kwikius/ultrasonic_wind_sensor/sensor_hardware/modified_reversing_sensor_circuit/filter.sch

## KiCad design sensor_hardware/modified_reversing_sensor_circuit/filter.sch (2021-09-10, an earlier design)

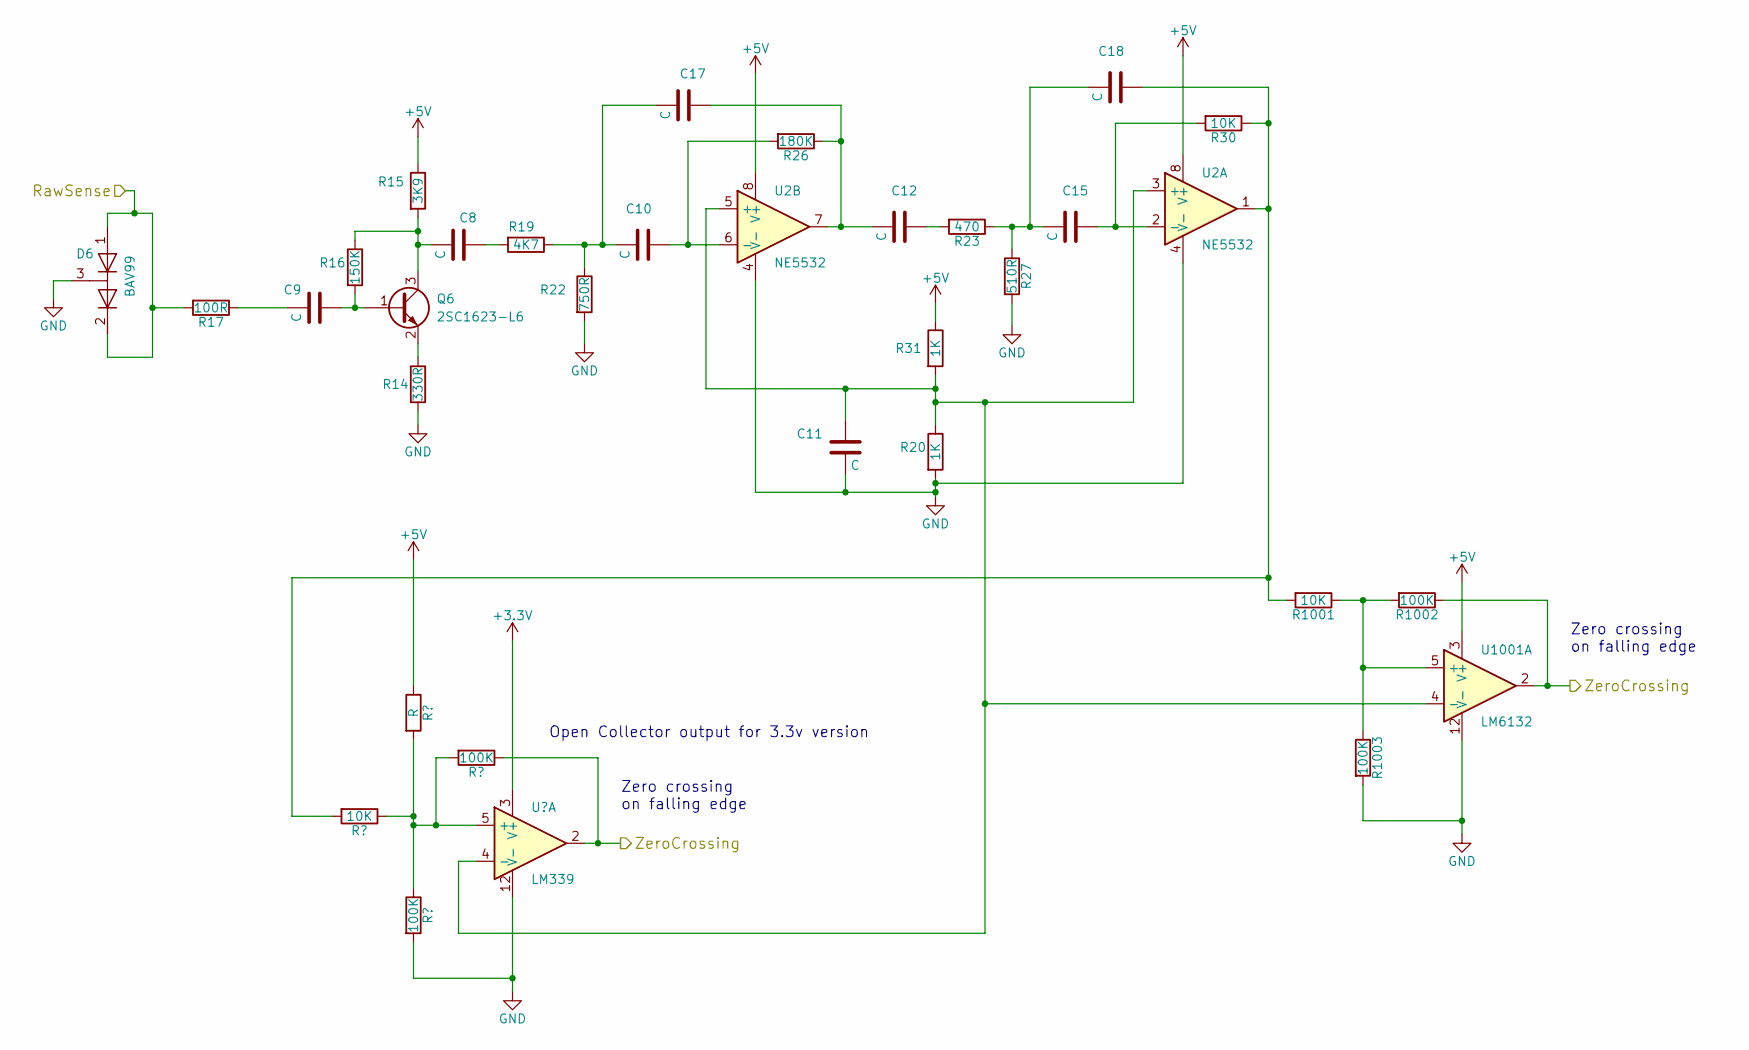
[picture p11: schematic filter.sch]

Parts:
C8, C9, C10, C11, C12, C15, C17, C18: C
D6: BAV99
Q6: 2SC1623-L6
R14: 330R
R15: 3K9
R16: 150K
R17: 100R
R19: 4K7
R20, R31: 1K
R22: 750R
R23: 470
R26: 180K
R27: 510R
R30, R1001: 10K
R1002, R1003: 100K
U2: NE5532
U1001: LM6132

Connections:
+5V: R15.1, R31.1, U2.8 (V+), U1001.3 (V+)
GND: C11.2, D6.3 (common), R14.2, R20.2, R22.2, R27.2, R1003.2, U2.4 (V-), U1001.12 (V-)
unnamed: C8.1, R19.2
unnamed: C8.2, Q6.3 (C), R15.2, R16.1
unnamed: C9.1, Q6.1 (B), R16.2
unnamed: C9.2, R17.1
unnamed: C10.1, R26.2, U2.6 (-)
unnamed: C10.2, C17.2, R19.1, R22.1
unnamed: C11.1, R20.1, R31.2, U2.3 (+), U2.5 (+), U1001.4 (-)
unnamed: C12.1, R23.2
unnamed: C12.2, C17.1, R26.1, U2.7
unnamed: C15.1, R30.2, U2.2 (-)
unnamed: C15.2, C18.2, R23.1, R27.1
unnamed: C18.1, R30.1, R1001.2, U2.1
unnamed: Q6.2 (E), R14.1
unnamed: R1001.1, R1002.2, R1003.1, U1001.5 (+)
RawSense: D6.1 (A), D6.2 (K), R17.2
ZeroCrossing: R1002.1, U1001.2

Notes on the sheet:
Zero crossing on falling edge
Open Collector output for 3.3v version
