kwikius/ultrasonic_wind_sensor/sensor_hardware/modified_reversing_sensor_circuit/sensor_drivers.sch

## KiCad design sensor_hardware/modified_reversing_sensor_circuit/sensor_drivers.sch (2021-09-10, an earlier design)

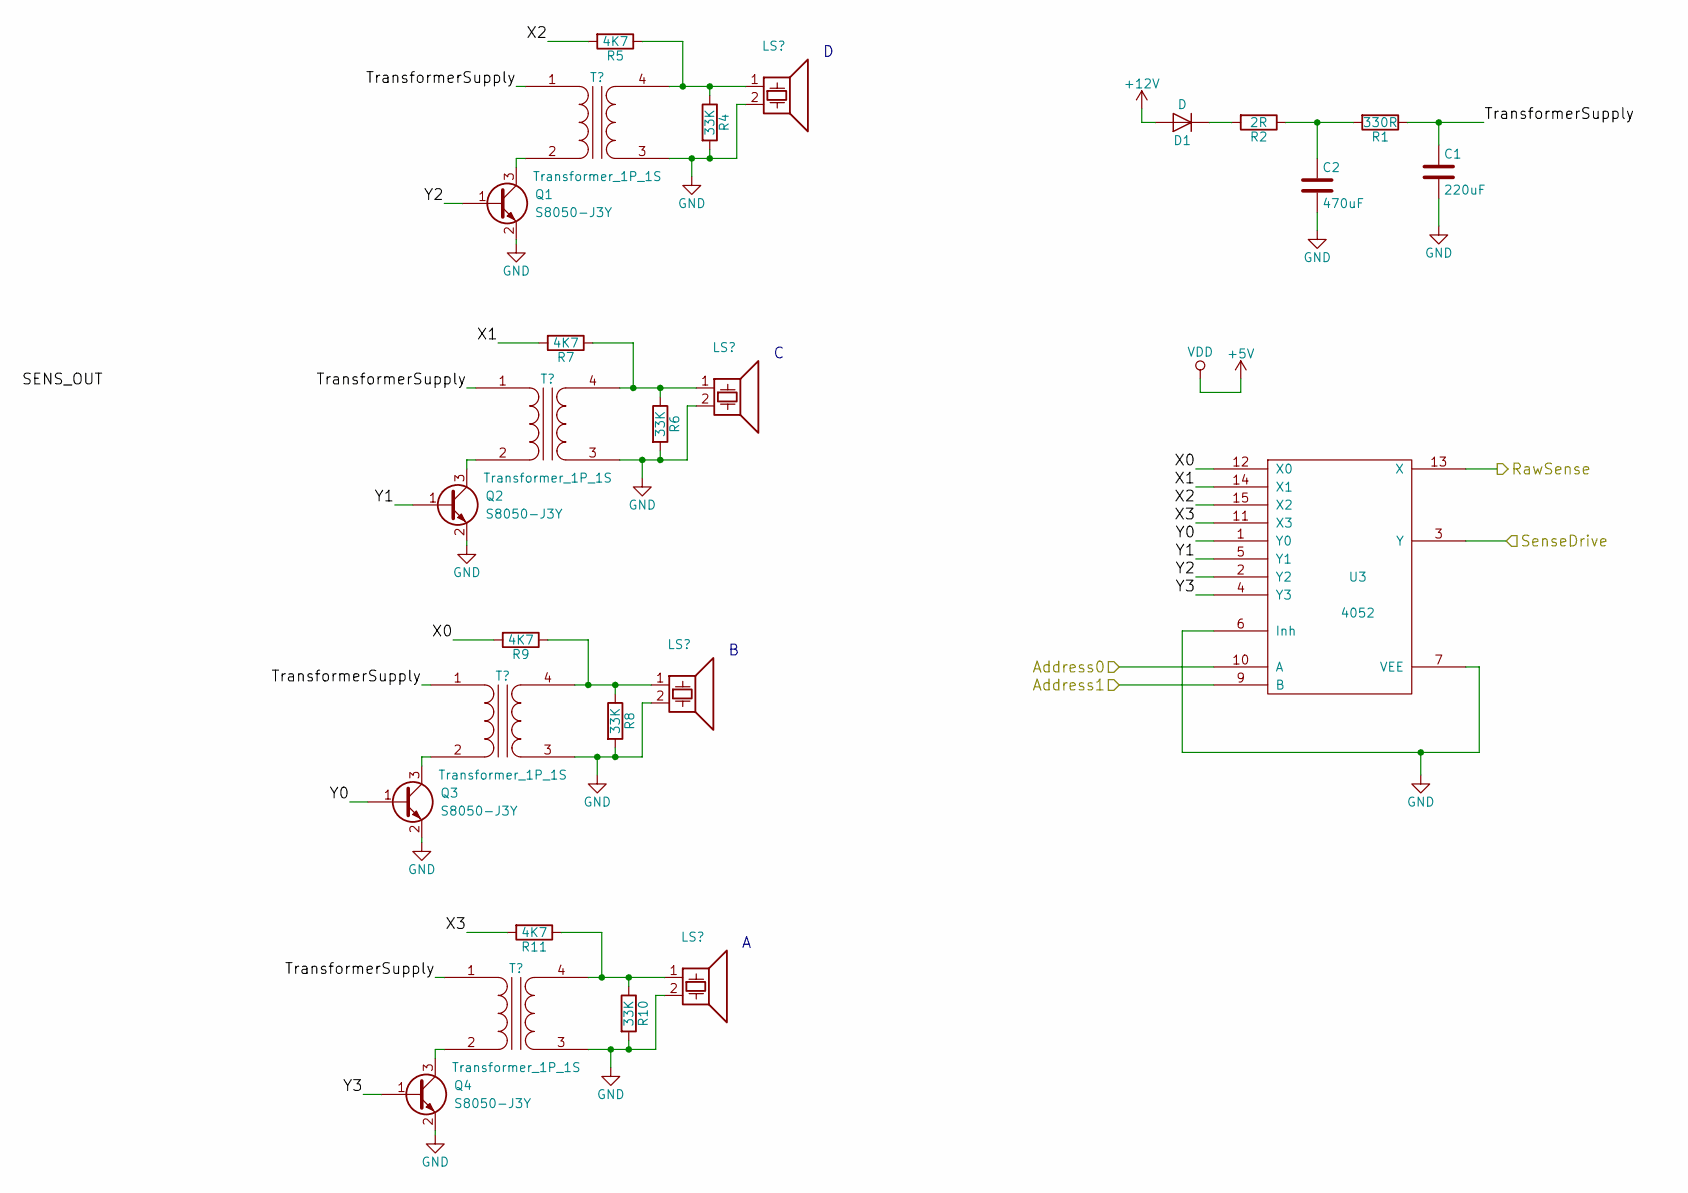
[picture p12: schematic sensor_drivers.sch]

Parts:
C1: 220uF
C2: 470uF
D1: D
Q1, Q2, Q3, Q4: S8050-J3Y
R1: 330R
R2: 2R
R4, R6, R8, R10: 33K
R5, R7, R9, R11: 4K7
U3: 4052

Connections:
+12V: D1.2 (A)
Address0: U3.10 (A)
Address1: U3.9 (B)
GND: C1.2, C2.2, Q1.2 (E), Q2.2 (E), Q3.2 (E), Q4.2 (E), R4.2, R6.2, R8.2, R10.2, U3.6 (Inh), U3.7 (VEE)
unnamed: C2.1, R1.2, R2.1
unnamed: D1.1 (K), R2.2
unnamed: R4.1, R5.1
unnamed: R6.1, R7.1
unnamed: R8.1, R9.1
unnamed: R10.1, R11.1
RawSense: U3.13 (X)
SenseDrive: U3.3 (Y)
TransformerSupply: C1.1, R1.1
X0: R9.2, U3.12 (X0)
X1: R7.2, U3.14 (X1)
X2: R5.2, U3.15 (X2)
X3: R11.2, U3.11 (X3)
Y0: Q3.1 (B), U3.1 (Y0)
Y1: Q2.1 (B), U3.5 (Y1)
Y2: Q1.1 (B), U3.2 (Y2)
Y3: Q4.1 (B), U3.4 (Y3)
