kwikius/ultrasonic_wind_sensor/sensor_hardware/modified_reversing_sensor_circuit_arduino/atmega328p_mcu.sch

## KiCad design sensor_hardware/modified_reversing_sensor_circuit_arduino/atmega328p_mcu.sch (2021-11-03, an earlier design)

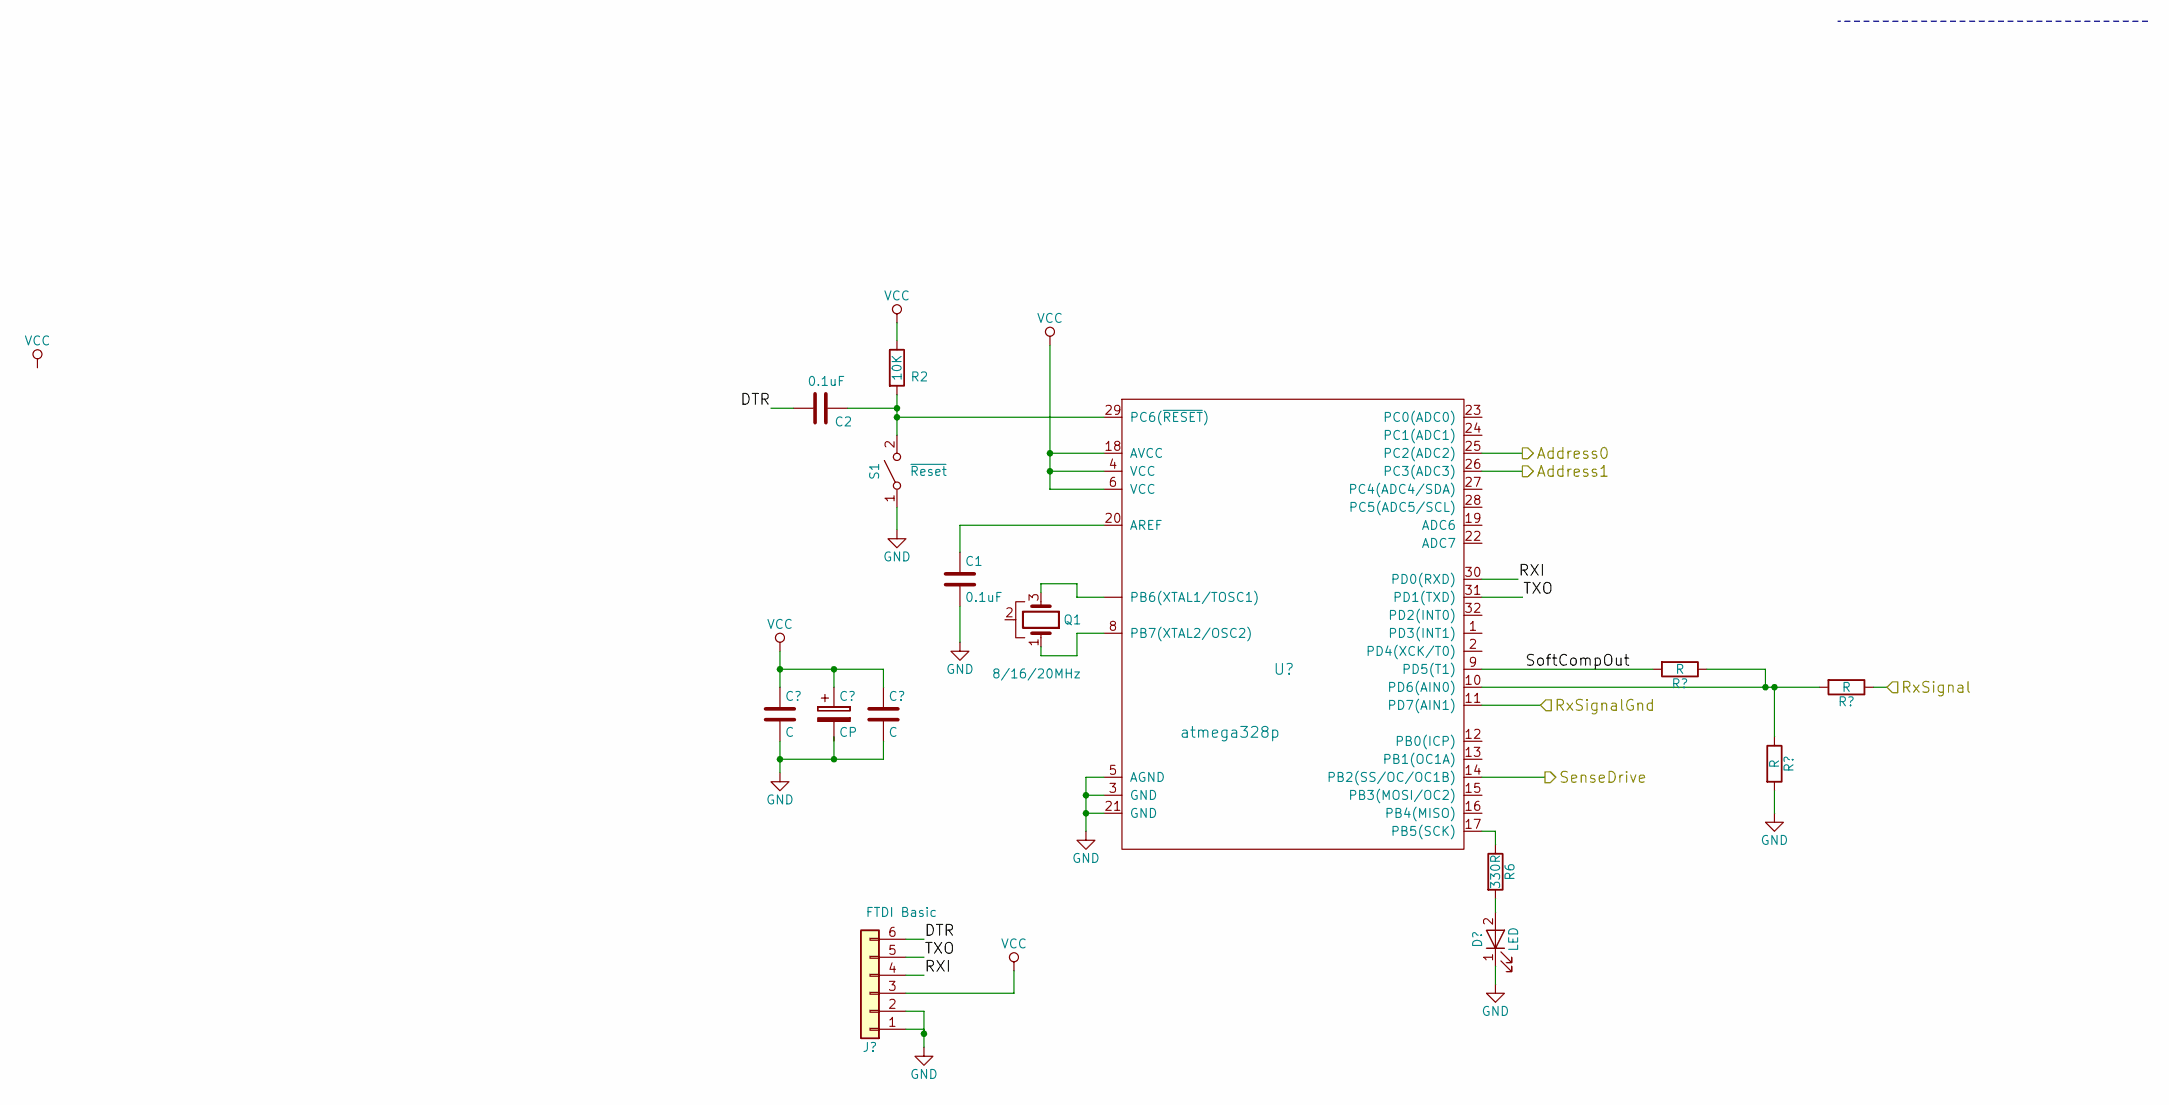
[picture p13: schematic atmega328p_mcu.sch]

Parts:
C1, C2: 0.1uF
Q1: 8/16/20MHz
R2: 10K
R6: 330R
S1: ~Reset

Connections:
DTR: C2.2
GND: C1.2, S1.1 (A)
unnamed: C2.1, R2.2, S1.2 (B)
VCC: R2.1
