kwikius/ultrasonic_wind_sensor/sensor_hardware/modified_reversing_sensor_circuit_arduino/wifi.sch

## KiCad design sensor_hardware/modified_reversing_sensor_circuit_arduino/wifi.sch (2021-11-03)

Schematic: wifi.sch

Parts:
C17: C
C18: CP
Q6, Q7: 2SK1336
R30: 4K7
R31, R32: 10K
SW2: SW_Push
U5: LM117_TO3; TO-3
U6: ESP-01
